makingdevices/MakerAxe-lite/Kicad/3d/ESP32-S3-WROOM-1-N8R2--3DModel-STEP-56544.STEP

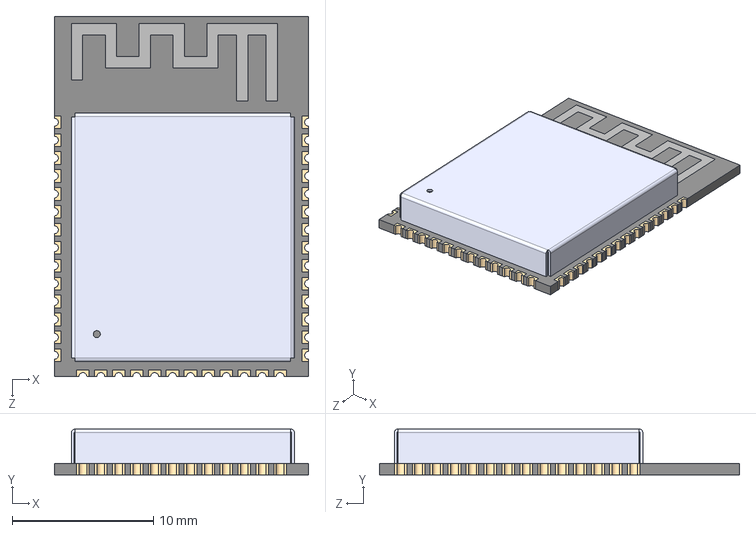
[picture p21: CAD file, 2024-12-18]
Kicad/3d/ESP32-S3-WROOM-1-N8R2--3DModel-STEP-56544.STEP
18.0 x 3.25 x 25.5 mm
