makingdevices/MakerAxe-lite/Kicad/3d/CUI_DEVICES_PJ-002AH.step

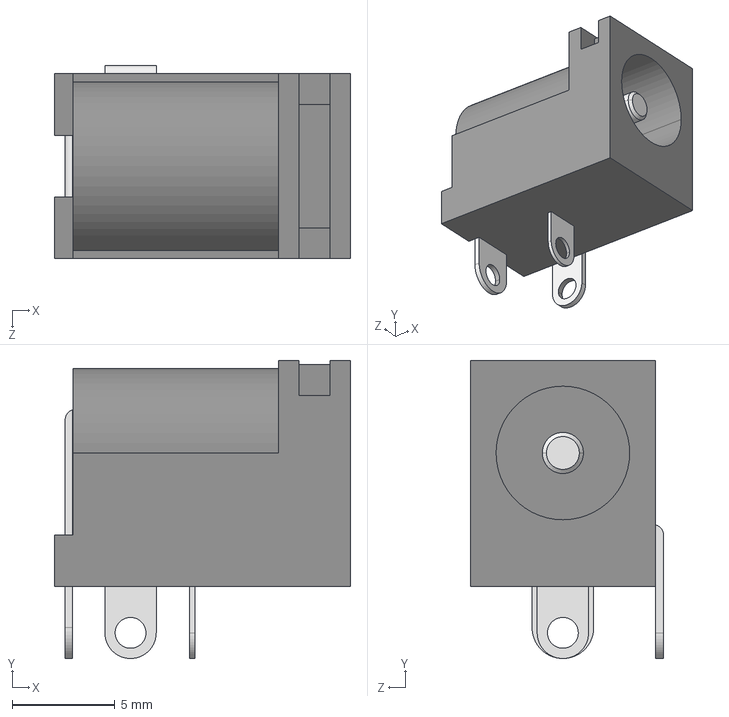
[picture p23: CAD file, 2024-12-18]
Kicad/3d/CUI_DEVICES_PJ-002AH.step
14.4 x 14.5 x 9.40 mm
