makingdevices/MakerAxe-lite/Kicad/3d/XRCGB27M120F3M10R0_MUR.step

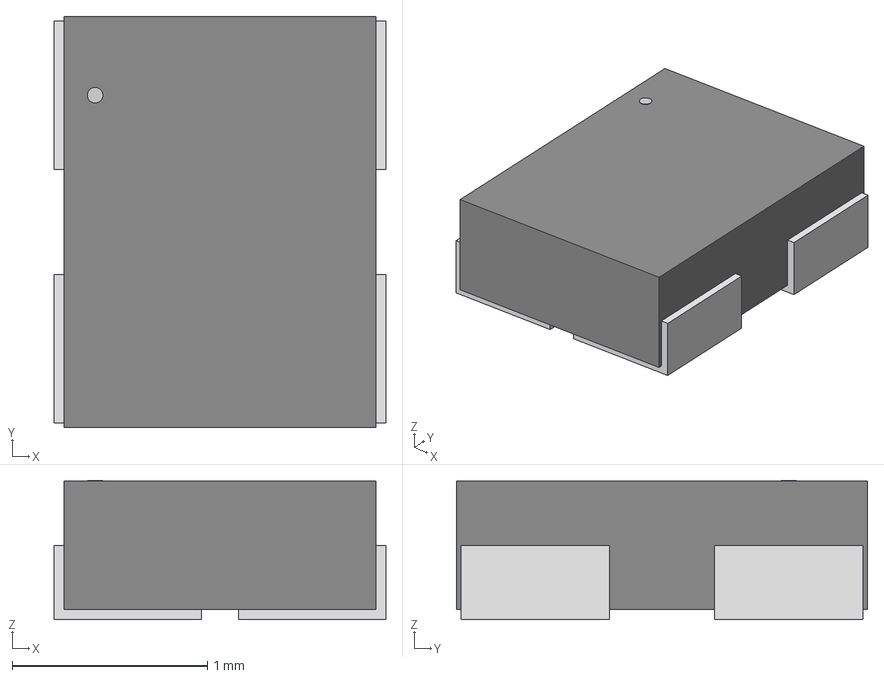
[picture p24: CAD file, 2024-12-18]
Kicad/3d/XRCGB27M120F3M10R0_MUR.step
1.70 x 2.11 x 0.714 mm
