makingdevices/MakerAxe-lite/Kicad/3d/IHLP2020CZ.step

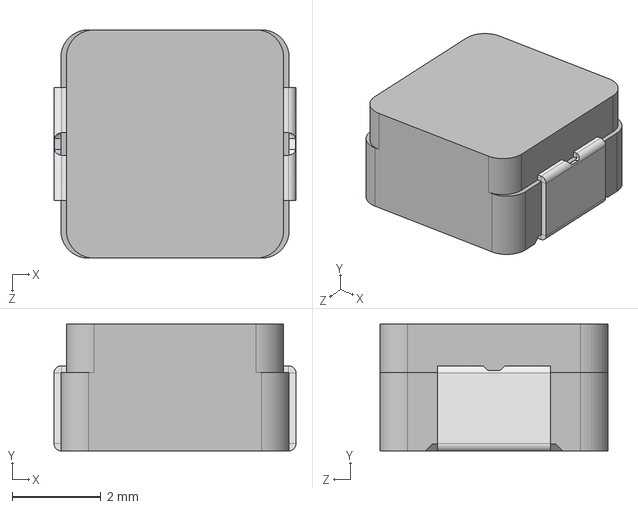
[picture p25: CAD file, 2024-12-18]
Kicad/3d/IHLP2020CZ.step
5.45 x 2.86 x 5.15 mm
