makingdevices/MakerAxe-lite/Kicad/3d/DISST7789-176x320.STEP

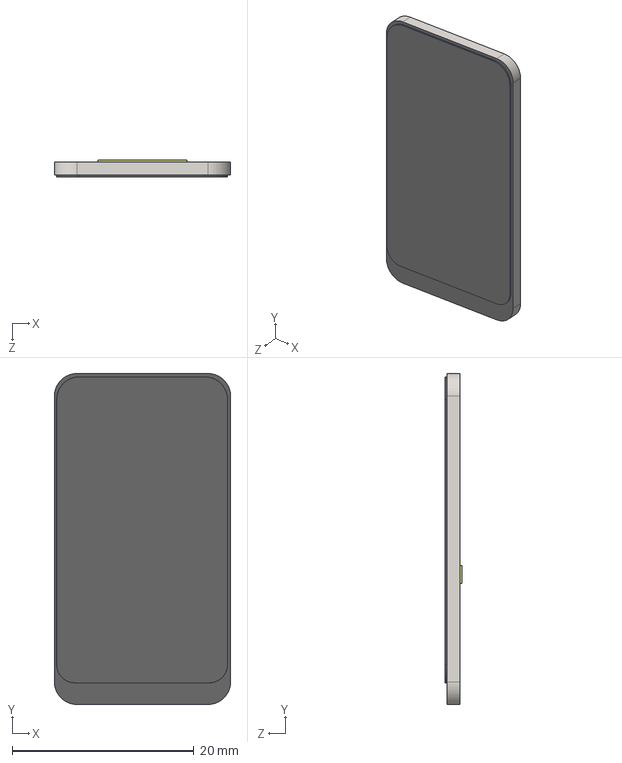
[picture p26: CAD file, 2024-12-18]
Kicad/3d/DISST7789-176x320.STEP
19.4 x 36.4 x 1.86 mm
