makingdevices/MakerAxe-lite/Kicad/3d/TSOT-23-5_RIT.step

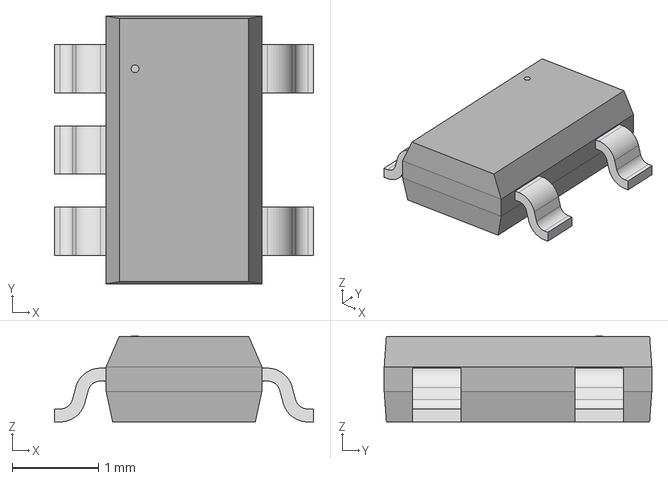
[picture p27: CAD file, 2024-12-18]
Kicad/3d/TSOT-23-5_RIT.step
3.00 x 3.10 x 0.993 mm
