makingdevices/MakerAxe-lite/Kicad/3d/54-00164.STEP

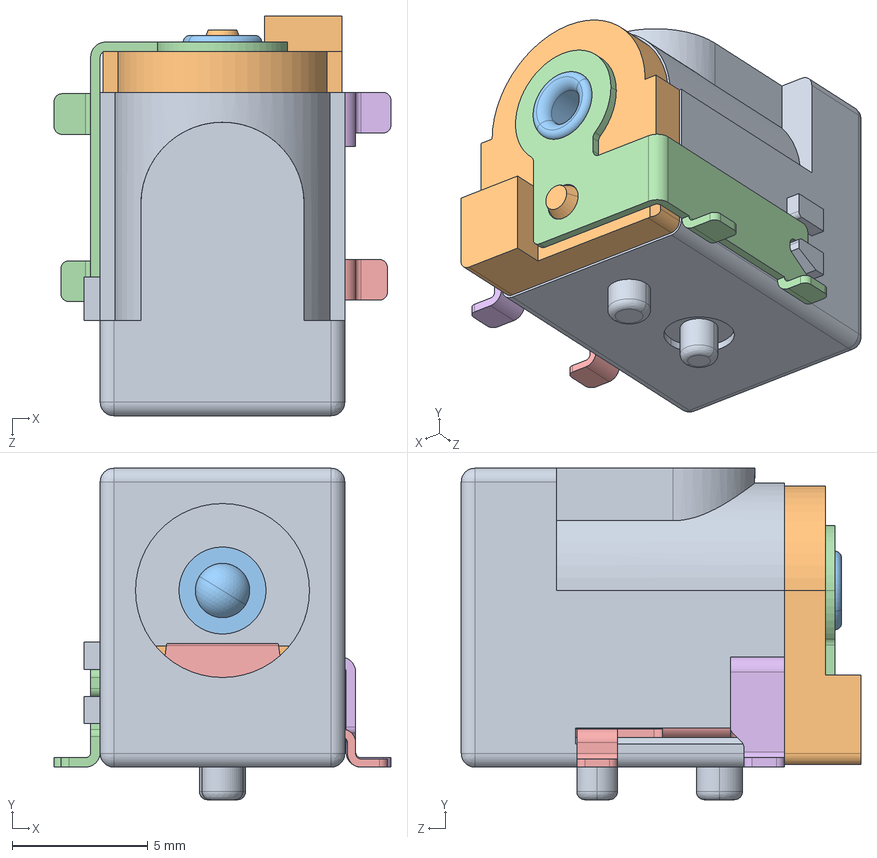
[picture p28: CAD file, 2024-12-18]
Kicad/3d/54-00164.STEP
12.4 x 12.2 x 14.7 mm
54-00164_shell
54-00164_insulator
54-00164_center
54-00164_center contact
54-00164_spring contact
54-00164_shell contact
