makingdevices/MakerAxe-lite/Kicad/3d/SMV_z90.stp

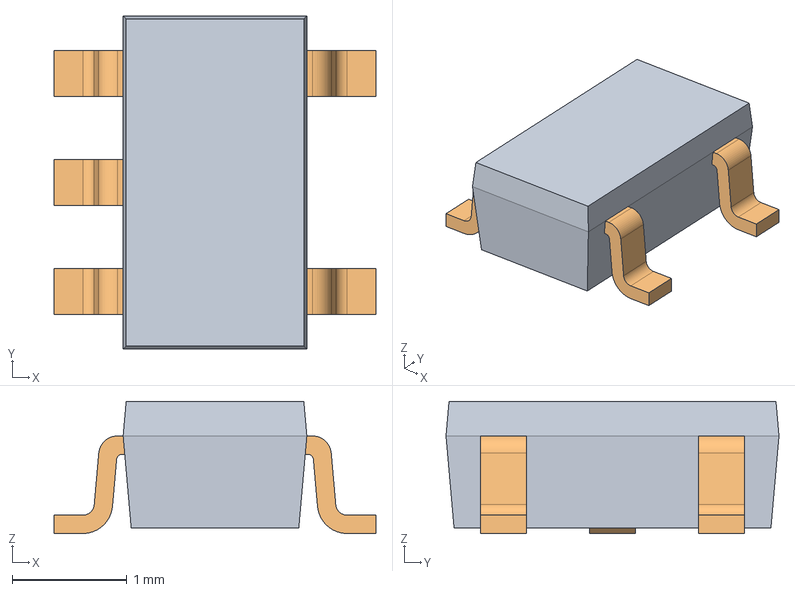
[picture p29: CAD file, 2024-12-18]
Kicad/3d/SMV_z90.stp
2.80 x 2.90 x 1.15 mm
