makingdevices/MakerAxe-lite/Kicad/3d/SPM6530T-R47M-HZ.stp

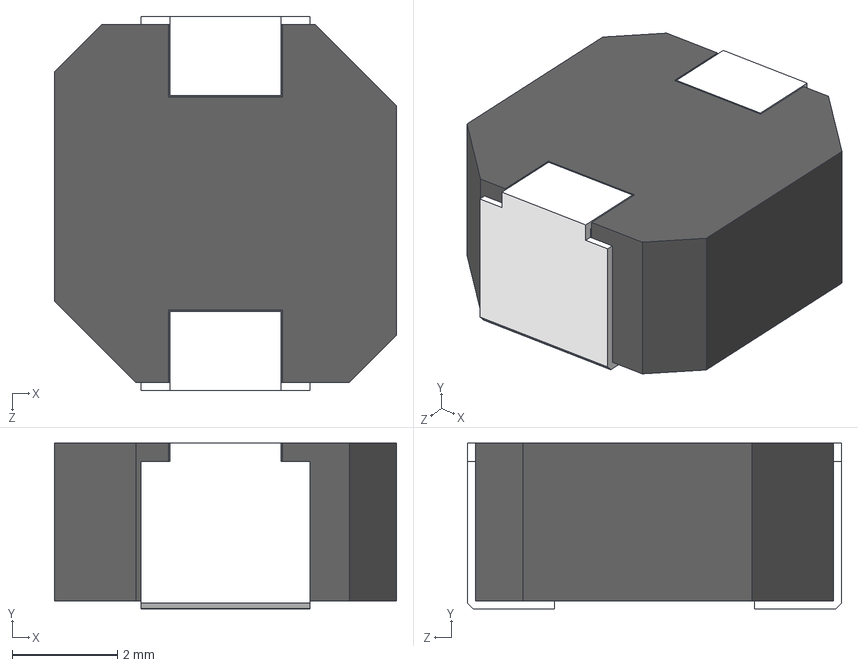
[picture p30: CAD file, 2024-12-18]
Kicad/3d/SPM6530T-R47M-HZ.stp
6.50 x 3.15 x 7.10 mm
