makingdevices/MakerAxe-lite/Kicad/3d/XTAL_SC32S-7PF20PPM_EPS.step

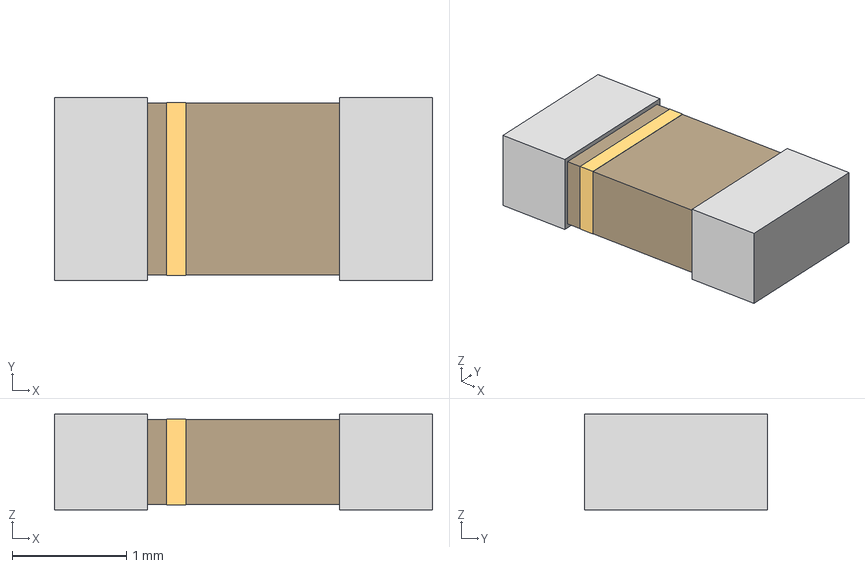
[picture p31: CAD file, 2024-12-18]
Kicad/3d/XTAL_SC32S-7PF20PPM_EPS.step
3.30 x 1.60 x 0.838 mm
