makingdevices/MakerAxe-lite/Kicad/3d/Bitaxe_Heatsink.step

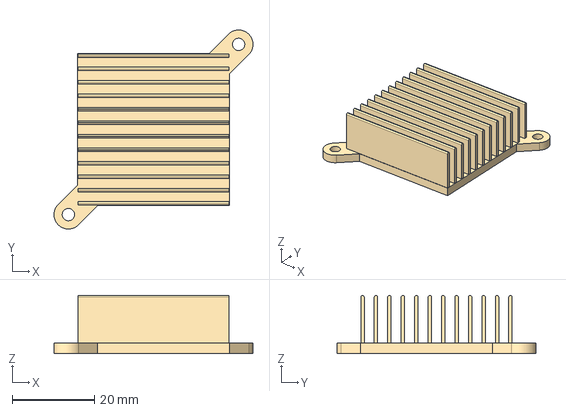
[picture p33: CAD file, 2024-12-18]
Kicad/3d/Bitaxe_Heatsink.step
48.4 x 48.4 x 14.1 mm
