makingdevices/MakerAxe-lite/Kicad/3d/USB_10118193-0001LF.STEP

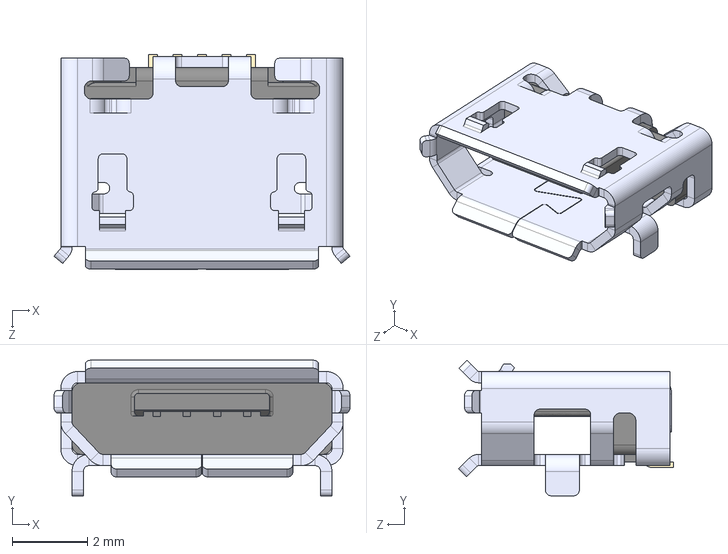
[picture p34: CAD file, 2024-12-18]
Kicad/3d/USB_10118193-0001LF.STEP
7.86 x 3.60 x 5.71 mm
