makingdevices/MakerAxe-lite/Kicad/3d/FP1006V2-R.STEP

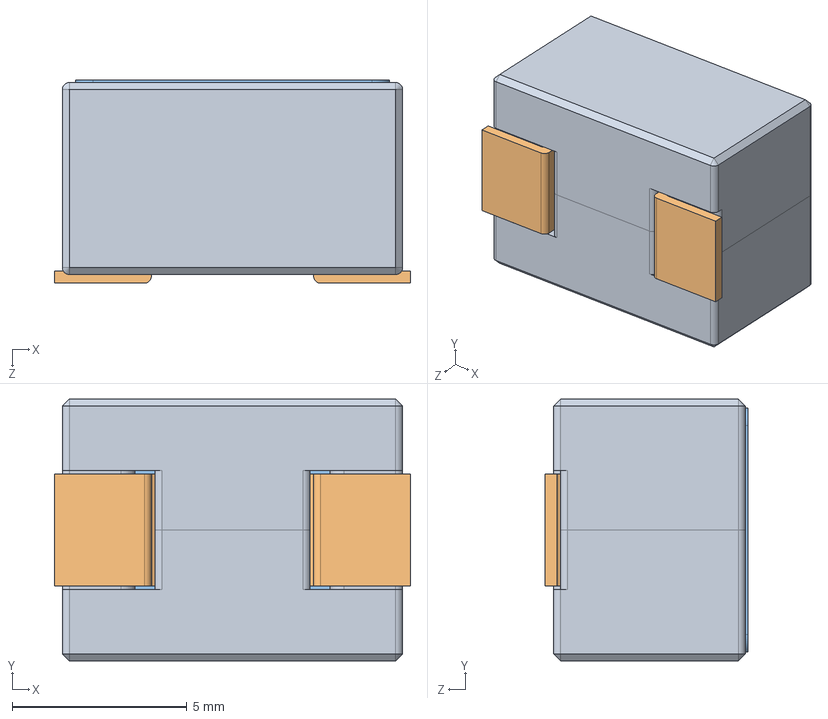
[picture p35: CAD file, 2024-12-18]
Kicad/3d/FP1006V2-R.STEP
10.2 x 7.50 x 5.83 mm
11150900A x 2
53134900A
Label for FP1006V2-R
