makingdevices/MakerAxe-lite/Kicad/3d/PTVS20VS1UR,115.stp

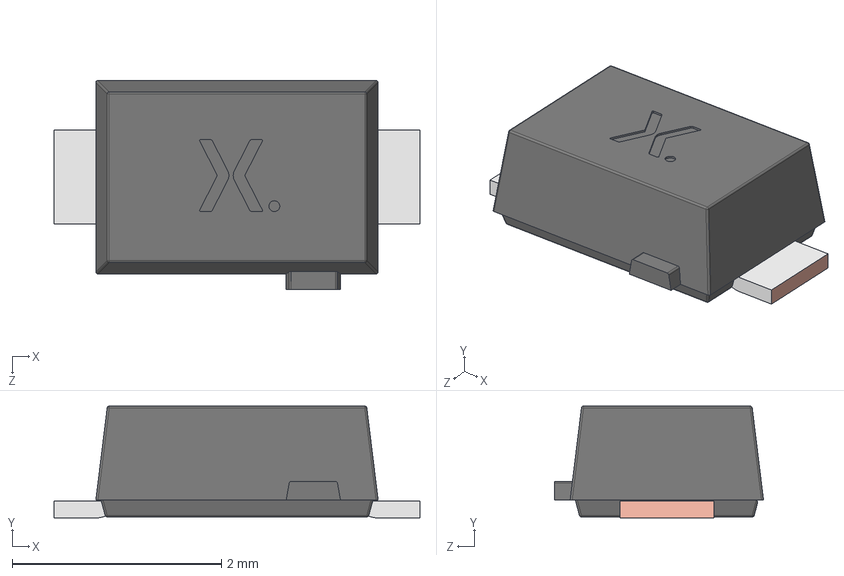
[picture p36: CAD file, 2024-12-18]
Kicad/3d/PTVS20VS1UR,115.stp
3.50 x 1.07 x 2.00 mm
SOD123W Lower body
SOD123W Lead x 2
SOD123W Upper body
