makingdevices/MakerAxe-lite/Kicad/3d/SW_CS1213AGF260_CRS.step

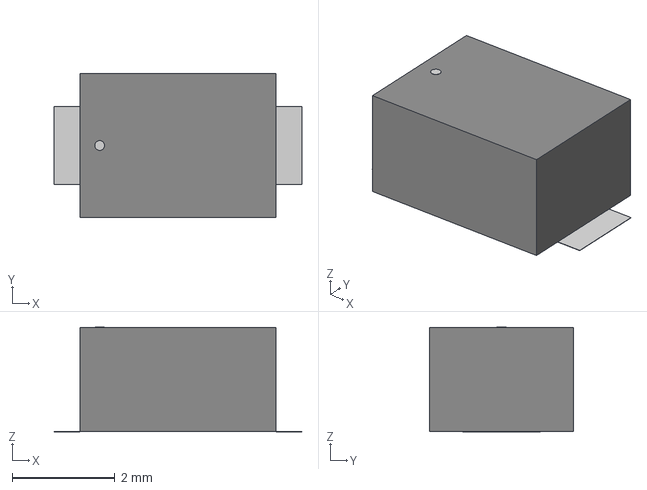
[picture p37: CAD file, 2024-12-18]
Kicad/3d/SW_CS1213AGF260_CRS.step
4.83 x 2.79 x 2.04 mm
