makingdevices/MakerAxe-lite/Kicad/3d/DQH0008A.stp

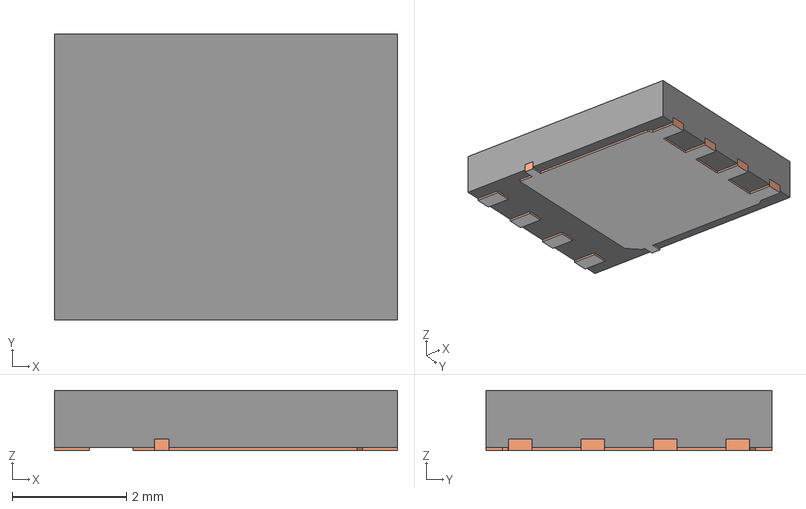
[picture p38: CAD file, 2024-12-18]
Kicad/3d/DQH0008A.stp
6.00 x 5.00 x 1.05 mm
BODY-SON
FRAME-DQH0008A
PIN1-ID
