makingdevices/MakerAxe-lite/Kicad/3d/CUI_DEVICES_PJ-037AH.step

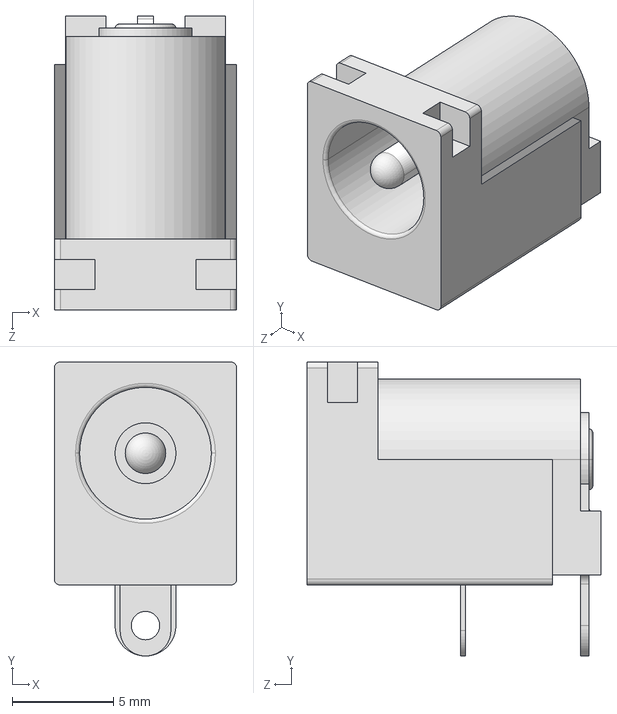
[picture p40: CAD file, 2024-12-18]
Kicad/3d/CUI_DEVICES_PJ-037AH.step
9.00 x 14.5 x 14.5 mm
