makingdevices/MakerAxe-lite/Kicad/3d/TS2940CW33_RPG.stp

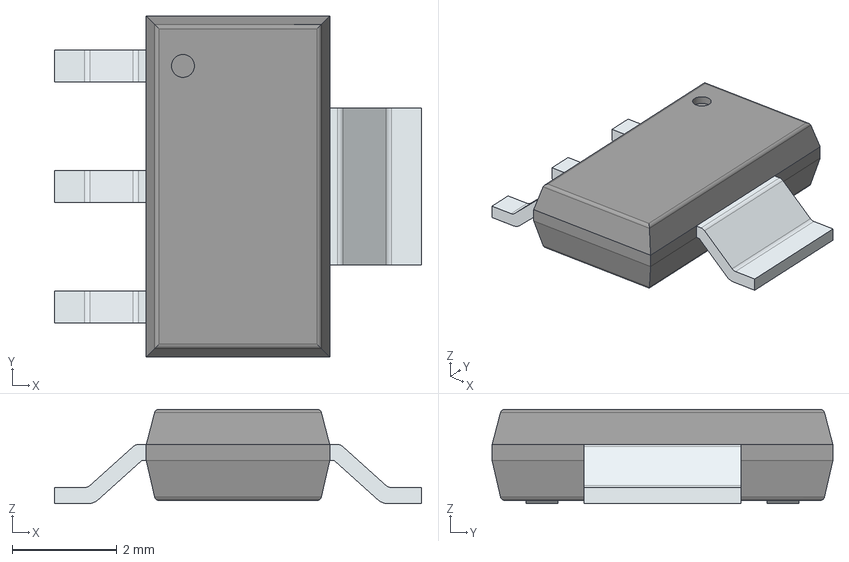
[picture p41: CAD file, 2024-12-18]
Kicad/3d/TS2940CW33_RPG.stp
7.00 x 6.50 x 1.80 mm
PinsArrayL
FilletPinR
