makingdevices/MakerAxe-lite/Kicad/3d/c-63862-1-r-3d.stp

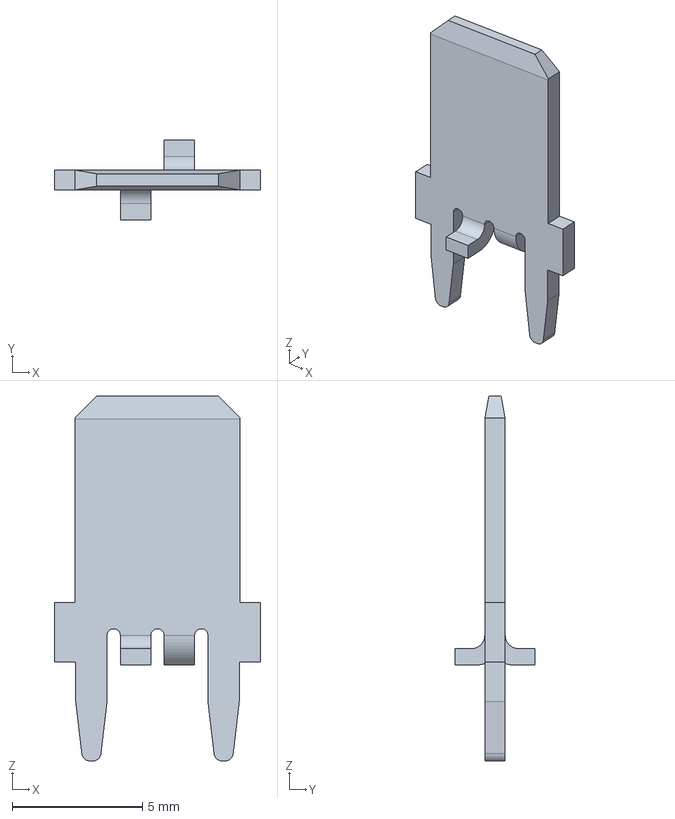
[picture p42: CAD file, 2024-12-18]
Kicad/3d/c-63862-1-r-3d.stp
7.92 x 3.07 x 14.0 mm
